Style71/FrequencyAnalyse/STM32Firmware/Src/adc.cpp

/**
  ******************************************************************************
  * File Name          : ADC.c
  * Description        : This file provides code for the configuration
  *                      of the ADC instances.
  ******************************************************************************
  * @attention
  *
  * <h2><center>&copy; Copyright (c) 2020 STMicroelectronics.
  * All rights reserved.</center></h2>
  *
  * This software component is licensed by ST under BSD 3-Clause license,
  * the "License"; You may not use this file except in compliance with the
  * License. You may obtain a copy of the License at:
  *                        opensource.org/licenses/BSD-3-Clause
  *
  ******************************************************************************
  */

/* Includes ------------------------------------------------------------------*/
#include "adc.h"
#include "usart.h"
ADC_HandleTypeDef hadc1;
DMA_HandleTypeDef hdma_adc1;

uint16_t ADCResult0[ADC_BUFFER_SIZE];
uint16_t ADCResult1[ADC_BUFFER_SIZE];
/**
  * @brief  DMA transfer complete callback. 
  * @param  hdma pointer to a DMA_HandleTypeDef structure that contains
  *                the configuration information for the specified DMA module.
  * @retval None
  */
static void ADC_DMAConvCplt(DMA_HandleTypeDef *hdma)
{
  /* Retrieve ADC handle corresponding to current DMA handle */
  ADC_HandleTypeDef *hadc = (ADC_HandleTypeDef *)((DMA_HandleTypeDef *)hdma)->Parent;

  /* Update state machine on conversion status if not in error state */
  if (HAL_IS_BIT_CLR(hadc->State, HAL_ADC_STATE_ERROR_INTERNAL | HAL_ADC_STATE_ERROR_DMA))
  {
    /* Update ADC state machine */
    SET_BIT(hadc->State, HAL_ADC_STATE_REG_EOC);

    /* Determine whether any further conversion upcoming on group regular   */
    /* by external trigger, continuous mode or scan sequence on going.      */
    /* Note: On STM32F7, there is no independent flag of end of sequence.   */
    /*       The test of scan sequence on going is done either with scan    */
    /*       sequence disabled or with end of conversion flag set to        */
    /*       of end of sequence.                                            */
    if (ADC_IS_SOFTWARE_START_REGULAR(hadc) &&
        (hadc->Init.ContinuousConvMode == DISABLE) &&
        (HAL_IS_BIT_CLR(hadc->Instance->SQR1, ADC_SQR1_L) ||
         HAL_IS_BIT_CLR(hadc->Instance->CR2, ADC_CR2_EOCS)))
    {
      /* Disable ADC end of single conversion interrupt on group regular */
      /* Note: Overrun interrupt was enabled with EOC interrupt in          */
      /* HAL_ADC_Start_IT(), but is not disabled here because can be used   */
      /* by overrun IRQ process below.                                      */
      __HAL_ADC_DISABLE_IT(hadc, ADC_IT_EOC);

      /* Set ADC state */
      CLEAR_BIT(hadc->State, HAL_ADC_STATE_REG_BUSY);

      if (HAL_IS_BIT_CLR(hadc->State, HAL_ADC_STATE_INJ_BUSY))
      {
        SET_BIT(hadc->State, HAL_ADC_STATE_READY);
      }
    }

    /* Conversion complete callback */
#if (USE_HAL_ADC_REGISTER_CALLBACKS == 1)
    hadc->ConvCpltCallback(hadc);
#else
    HAL_ADC_ConvCpltCallback(hadc);
#endif /* USE_HAL_ADC_REGISTER_CALLBACKS */
  }
  else /* DMA and-or internal error occurred */
  {
    if ((hadc->State & HAL_ADC_STATE_ERROR_INTERNAL) != 0UL)
    {
      /* Call HAL ADC Error Callback function */
#if (USE_HAL_ADC_REGISTER_CALLBACKS == 1)
      hadc->ErrorCallback(hadc);
#else
      HAL_ADC_ErrorCallback(hadc);
#endif /* USE_HAL_ADC_REGISTER_CALLBACKS */
    }
    else
    {
      /* Call DMA error callback */
      hadc->DMA_Handle->XferErrorCallback(hdma);
    }
  }
}

/**
  * @brief  DMA error callback 
  * @param  hdma pointer to a DMA_HandleTypeDef structure that contains
  *                the configuration information for the specified DMA module.
  * @retval None
  */
static void ADC_DMAError(DMA_HandleTypeDef *hdma)
{
  ADC_HandleTypeDef *hadc = (ADC_HandleTypeDef *)((DMA_HandleTypeDef *)hdma)->Parent;
  hadc->State = HAL_ADC_STATE_ERROR_DMA;
  /* Set ADC error code to DMA error */
  hadc->ErrorCode |= HAL_ADC_ERROR_DMA;
  /* Error callback */
#if (USE_HAL_ADC_REGISTER_CALLBACKS == 1)
  hadc->ErrorCallback(hadc);
#else
  HAL_ADC_ErrorCallback(hadc);
#endif /* USE_HAL_ADC_REGISTER_CALLBACKS */
}

/**
  * @brief  Enables ADC DMA request after last transfer (Single-ADC mode) and enables ADC peripheral  
  * @param  hadc pointer to a ADC_HandleTypeDef structure that contains
  *         the configuration information for the specified ADC.
  * @param  pData The destination Buffer address.
  * @param  Length The length of data to be transferred from ADC peripheral to memory.
  * @retval HAL status
  */
HAL_StatusTypeDef ADC_Start_DMA(ADC_HandleTypeDef *hadc, uint32_t *pFirstData, uint32_t *pSecondData, uint32_t Length)
{
  __IO uint32_t counter = 0;

  /* Check the parameters */
  assert_param(IS_FUNCTIONAL_STATE(hadc->Init.ContinuousConvMode));
  assert_param(IS_ADC_EXT_TRIG_EDGE(hadc->Init.ExternalTrigConvEdge));

  /* Process locked */
  __HAL_LOCK(hadc);

  /* Enable the ADC peripheral */
  /* Check if ADC peripheral is disabled in order to enable it and wait during 
     Tstab time the ADC's stabilization */
  if ((hadc->Instance->CR2 & ADC_CR2_ADON) != ADC_CR2_ADON)
  {
    /* Enable the Peripheral */
    __HAL_ADC_ENABLE(hadc);

    /* Delay for ADC stabilization time */
    /* Compute number of CPU cycles to wait for */
    counter = (ADC_STAB_DELAY_US * (SystemCoreClock / 1000000));
    while (counter != 0)
    {
      counter--;
    }
  }

  /* Start conversion if ADC is effectively enabled */
  if (HAL_IS_BIT_SET(hadc->Instance->CR2, ADC_CR2_ADON))
  {
    /* Set ADC state                                                          */
    /* - Clear state bitfield related to regular group conversion results     */
    /* - Set state bitfield related to regular group operation                */
    ADC_STATE_CLR_SET(hadc->State,
                      HAL_ADC_STATE_READY | HAL_ADC_STATE_REG_EOC | HAL_ADC_STATE_REG_OVR,
                      HAL_ADC_STATE_REG_BUSY);

    /* If conversions on group regular are also triggering group injected,    */
    /* update ADC state.                                                      */
    if (READ_BIT(hadc->Instance->CR1, ADC_CR1_JAUTO) != RESET)
    {
      ADC_STATE_CLR_SET(hadc->State, HAL_ADC_STATE_INJ_EOC, HAL_ADC_STATE_INJ_BUSY);
    }

    /* State machine update: Check if an injected conversion is ongoing */
    if (HAL_IS_BIT_SET(hadc->State, HAL_ADC_STATE_INJ_BUSY))
    {
      /* Reset ADC error code fields related to conversions on group regular */
      CLEAR_BIT(hadc->ErrorCode, (HAL_ADC_ERROR_OVR | HAL_ADC_ERROR_DMA));
    }
    else
    {
      /* Reset ADC all error code fields */
      ADC_CLEAR_ERRORCODE(hadc);
    }

    /* Process unlocked */
    /* Unlock before starting ADC conversions: in case of potential           */
    /* interruption, to let the process to ADC IRQ Handler.                   */
    __HAL_UNLOCK(hadc);

    /* Set the DMA transfer complete callback */
    hadc->DMA_Handle->XferCpltCallback = ADC_DMAConvCplt;

    /* Set the DMA half transfer complete callback */
    hadc->DMA_Handle->XferHalfCpltCallback = NULL;

    /* Set the DMA error callback */
    hadc->DMA_Handle->XferErrorCallback = ADC_DMAError;

    /* Manage ADC and DMA start: ADC overrun interruption, DMA start, ADC     */
    /* start (in case of SW start):                                           */

    /* Clear regular group conversion flag and overrun flag */
    /* (To ensure of no unknown state from potential previous ADC operations) */
    __HAL_ADC_CLEAR_FLAG(hadc, ADC_FLAG_EOC | ADC_FLAG_OVR);

    /* Enable ADC overrun interrupt */
    __HAL_ADC_ENABLE_IT(hadc, ADC_IT_OVR);

    /* Enable ADC DMA mode */
    hadc->Instance->CR2 |= ADC_CR2_DMA;

    /* Start the DMA channel */
    HAL_DMAEx_MultiBufferStart_IT(hadc->DMA_Handle, (uint32_t)&hadc->Instance->DR, (uint32_t)pFirstData, (uint32_t)pSecondData, Length);

    /* if no external trigger present enable software conversion of regular channels */
    if ((hadc->Instance->CR2 & ADC_CR2_EXTEN) == RESET)
    {
      /* Enable the selected ADC software conversion for regular group */
      hadc->Instance->CR2 |= (uint32_t)ADC_CR2_SWSTART;
    }
  }

  /* Return function status */
  return HAL_OK;
}

/* ADC1 init function */
void MX_ADC1_Init(void)
{
  ADC_ChannelConfTypeDef sConfig = {0};

  /** Configure the global features of the ADC (Clock, Resolution, Data Alignment and number of conversion) 
  */
  hadc1.Instance = ADC1;
  hadc1.Init.ClockPrescaler = ADC_CLOCK_SYNC_PCLK_DIV8;
  hadc1.Init.Resolution = ADC_RESOLUTION_12B;
  hadc1.Init.ScanConvMode = ADC_SCAN_DISABLE;
  hadc1.Init.ContinuousConvMode = DISABLE;
  hadc1.Init.DiscontinuousConvMode = DISABLE;
  hadc1.Init.ExternalTrigConvEdge = ADC_EXTERNALTRIGCONVEDGE_RISING;
  hadc1.Init.ExternalTrigConv = ADC_EXTERNALTRIGCONV_T2_CC2;
  hadc1.Init.DataAlign = ADC_DATAALIGN_RIGHT;
  hadc1.Init.NbrOfConversion = 1;
  hadc1.Init.DMAContinuousRequests = ENABLE;
  hadc1.Init.EOCSelection = ADC_EOC_SINGLE_CONV;
  if (HAL_ADC_Init(&hadc1) != HAL_OK)
  {
    Error_Handler();
  }
  /** Configure for the selected ADC regular channel its corresponding rank in the sequencer and its sample time. 
  */
  sConfig.Channel = ADC_CHANNEL_3;
  sConfig.Rank = ADC_REGULAR_RANK_1;
  sConfig.SamplingTime = ADC_SAMPLETIME_144CYCLES;
  if (HAL_ADC_ConfigChannel(&hadc1, &sConfig) != HAL_OK)
  {
    Error_Handler();
  }
  //currentBuffer = ADCResult0;
  HAL_NVIC_SetPriority(ADC_IRQn, 2, 0);
  HAL_NVIC_EnableIRQ(ADC_IRQn);

  ADC_Start_DMA(&hadc1, (uint32_t *)ADCResult0, (uint32_t *)ADCResult1, ADC_BUFFER_SIZE);
}

void HAL_ADC_MspInit(ADC_HandleTypeDef *adcHandle)
{

  GPIO_InitTypeDef GPIO_InitStruct = {0};
  if (adcHandle->Instance == ADC1)
  {
    /* ADC1 clock enable */
    __HAL_RCC_ADC1_CLK_ENABLE();

    __HAL_RCC_GPIOA_CLK_ENABLE();
    /**ADC1 GPIO Configuration    
    PA3     ------> ADC1_IN3 
    */
    GPIO_InitStruct.Pin = GPIO_PIN_3;
    GPIO_InitStruct.Mode = GPIO_MODE_ANALOG;
    GPIO_InitStruct.Pull = GPIO_NOPULL;
    HAL_GPIO_Init(GPIOA, &GPIO_InitStruct);

    /* ADC1 DMA Init */
    /* ADC1 Init */
    hdma_adc1.Instance = DMA2_Stream0;
    hdma_adc1.Init.Channel = DMA_CHANNEL_0;
    hdma_adc1.Init.Direction = DMA_PERIPH_TO_MEMORY;
    hdma_adc1.Init.PeriphInc = DMA_PINC_DISABLE;
    hdma_adc1.Init.MemInc = DMA_MINC_ENABLE;
    hdma_adc1.Init.PeriphDataAlignment = DMA_PDATAALIGN_HALFWORD;
    hdma_adc1.Init.MemDataAlignment = DMA_MDATAALIGN_HALFWORD;
    hdma_adc1.Init.Mode = DMA_NORMAL;
    hdma_adc1.Init.Priority = DMA_PRIORITY_VERY_HIGH;
    hdma_adc1.Init.FIFOMode = DMA_FIFOMODE_ENABLE;
    hdma_adc1.Init.FIFOThreshold = DMA_FIFO_THRESHOLD_3QUARTERSFULL;
    hdma_adc1.Init.MemBurst = DMA_MBURST_SINGLE;
    hdma_adc1.Init.PeriphBurst = DMA_PBURST_SINGLE;
    if (HAL_DMA_Init(&hdma_adc1) != HAL_OK)
    {
      Error_Handler();
    }

    __HAL_LINKDMA(adcHandle, DMA_Handle, hdma_adc1);

    /* USER CODE BEGIN ADC1_MspInit 1 */
    /*__HAL_DMA_DISABLE(&hdma_adc1);
    hdma_adc1.Instance->M0AR = (uint32_t)((void *)ADCResult0);
    hdma_adc1.Instance->M1AR = (uint32_t)((void *)ADCResult1);
    // Enable double buffer mode.
    SET_BIT(hdma_adc1.Instance->CR, DMA_SxCR_DBM);
    CLEAR_BIT(hdma_adc1.Instance->CR, DMA_SxCR_CT);
    __HAL_DMA_ENABLE(&hdma_adc1);*/
    /* USER CODE END ADC1_MspInit 1 */
  }
}

void HAL_ADC_MspDeInit(ADC_HandleTypeDef *adcHandle)
{

  if (adcHandle->Instance == ADC1)
  {
    /* Peripheral clock disable */
    __HAL_RCC_ADC1_CLK_DISABLE();

    /**ADC1 GPIO Configuration    
    PA3     ------> ADC1_IN3 
    */
    HAL_GPIO_DeInit(GPIOA, GPIO_PIN_3);

    /* ADC1 DMA DeInit */
    HAL_DMA_DeInit(adcHandle->DMA_Handle);
  }
}

/* USER CODE BEGIN 1 */
/*void HAL_ADC_ConvCpltCallback(ADC_HandleTypeDef *hadc)
{
  if (hadc->Instance == ADC1)
  {
    sampleCount += 3600;
    USART_Printf(&huart2, "%llu samples convert complete.\n", sampleCount);
    if (currentBuffer == ADCResult0)
      currentBuffer = ADCResult1;
    else
      currentBuffer = ADCResult0;
  }
}*/
/* USER CODE END 1 */

/************************ (C) COPYRIGHT STMicroelectronics *****END OF FILE****/
