Style71/FrequencyAnalyse/STM32Firmware/Src/SysTime.cpp

/**
  ******************************************************************************
  * File Name       : SysTime.c
  * Description     : System time base realised by systick timer.
	* Author					: Qi Yang
	* Date						: June, 08, 2020
  ******************************************************************************
  */
/* Includes ------------------------------------------------------------------*/
#include "SysTime.h"
#include "main.h"

#define TICKS_PER_US 216 // Equals to SystemCoreClock/1M

static uint64_t ullSysTicks = 0;
static uint64_t ullLastSysTicks;
uint64_t ullSysTimeUs = 0;

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
